AlessioSavelli/Controllo-Accessi/Firmware/Relese/Interfaccia Software/Risultato Finale.png

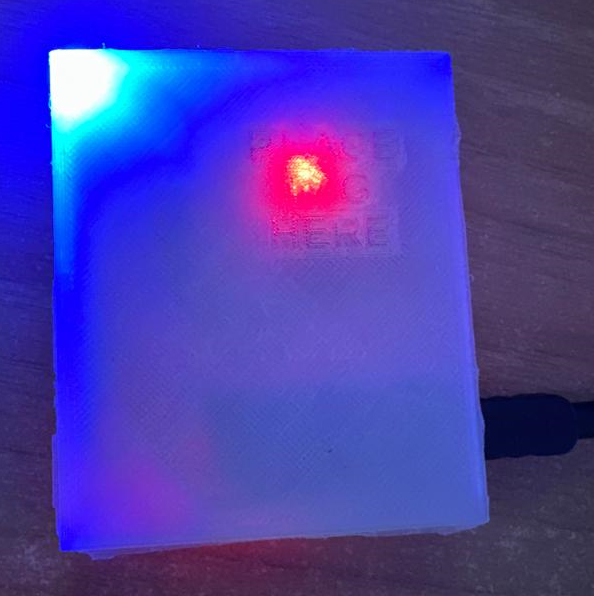
Firmware/Relese/Interfaccia Software/Risultato Finale.png
