AlessioSavelli/Controllo-Accessi/Firmware/Relese/Interfaccia Software/Schema.jpg

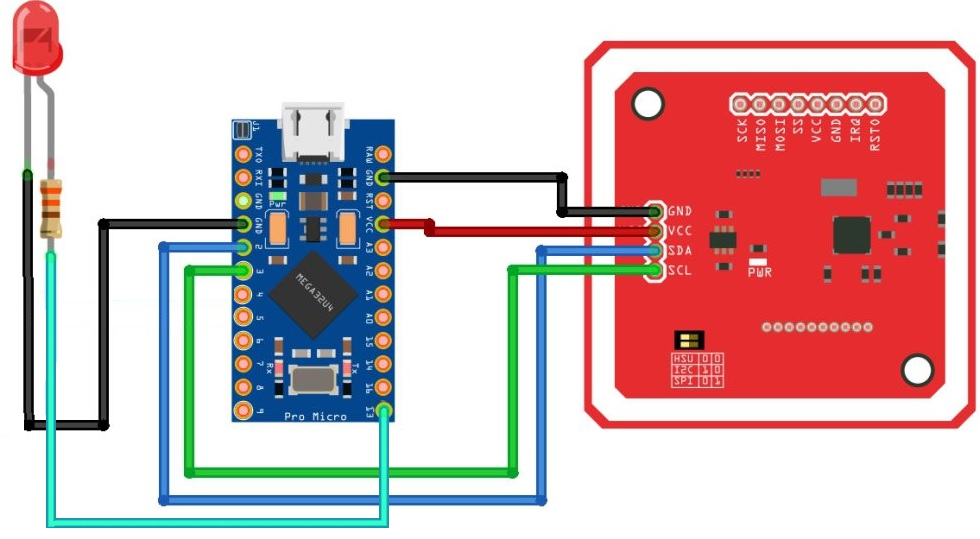
Firmware/Relese/Interfaccia Software/Schema.jpg
