AlessioSavelli/Controllo-Accessi/Firmware/Relese/V1.0.0/Main/Macro.h

/*    Macro di Alessio Savelli.       Create il 06/2022 e aggiornate al 01/2023
 *    Vers. : V1.0.1
 * Definisco delle macro generiche che vanno bene per tutto i moduli
 * N.B Ogni modulo/funzione può avere le sue macro specifiche solo per lei. Sono tutte dichiarata nei file .h o all'inizio delle funzioni
 */

//Definisco dei valori da uare per le macro
#define MACRO_TIMER_IS_NULL 0x00
#define MACRO_TIMER_INSTANTRIGGER_VALUE 0x01

#define MACRO_TIMER_TRIGER true
#define MACRO_TIMER_RUNING false

//----Definisco un Delay da usare per i core nel freertos---
#define TASKDELAY(MS) vTaskDelay(MS / portTICK_RATE_MS);
//------

//----Definisco Macro per gestire i timer----                                                                                             |ritorna true o false in base se il timer si triggera o no           |
#define IS_DELAYED(TIMER, MY_TIME) (((unsigned long)TIMER != MACRO_TIMER_IS_NULL) ? (((unsigned long)TIMER == MACRO_TIMER_INSTANTRIGGER_VALUE) ? MACRO_TIMER_TRIGER : ((millis() - ((unsigned long)TIMER)) >= MY_TIME)) : MACRO_TIMER_RUNING)  //Gestisce l'instant trigger e i timer inizializzati
#define START_TIMER(TIMER) (TIMER = millis())
#define STOP_TIMER(TIMER) (TIMER = MACRO_TIMER_IS_NULL)
#define ISALIVE_TIMER(TIMER) (TIMER != MACRO_TIMER_IS_NULL)
#define INSTANT_TRIGGER_TIMER(TIMER) (TIMER = MACRO_TIMER_INSTANTRIGGER_VALUE)  //Serve per avviare gia' il trigger del timer per la tempistica indicata in value
//-------------
//-----Definisco le macro per counter----
#define RESET_COUNTER(counter) (counter = 0)
//----
//----Definsico le macro per i buffer circolare---
#define CIRC_BUFFER_MULTISCROLL(index, scroll, maxItem) (index = (index + scroll) % maxItem)
#define CIRC_BUFFER_ONESCROLL(index, maxItem) (CIRC_BUFFER_MULTISCROLL(index, 1, maxItem))
#define REMOVE_FROM_INDEX(index, len) (index -= len)
#define ADD_TO_INDEX(index, len) (index += len)
//------
//-----Definisco le macro per gestire i bit----
#define BITMASK8(bitnum) (1 << bitnum)
#define GETBIT8(val, bitnum) ((val & BITMASK8(bitnum)) != 0)
#define BUILDBITMASK8(b7, b6, b5, b4, b3, b2, b1, b0) ((b0) | (b1 << 1) | (b2 << 2) | (b3 << 3) | (b4 << 4) | (b5 << 5) | (b6 << 6) | (b7 << 7))
#define CHECKBITMASK(val, bitmask) ((val & bitmask) == bitmask)
#define BITMASKRESET(bitmask) (bitmask = 0x00)
//----


//---Definisco macro per le conversione dei tempi
#define SECONDS 1000
#define MINUTES 60 * SECONDS
//------

//--Definisco macro per la conversione dei byte
#define KByte 1024
#define MByte 1024 * KByte
//----------

//--Definisco macro per la conversione in Hertz
#define KHz 1000
#define MHz 100000
//-----

//---Convert millis to format time
String _MY_MACRO_CONVERTION_TIME1(unsigned long time_to_convert) {
  unsigned long times = millis();
  int millisec = times % 100;
  int tseconds = times / 1000;
  int tminutes = tseconds / 60;
  int seconds = tseconds % 60;
  int thour = tminutes / 60;
  return "Time: " + String(thour, DEC) + ":" + String(tminutes, DEC) + ":" + String(seconds, DEC);
}

#define TIMEFORMAT_MILLIS _MY_MACRO_CONVERTION_TIME1(millis())
#define TIMEFORMAT_MILLIS_CHAR _MY_MACRO_CONVERTION_TIME1(millis()).c_str()

#define TIMEFORMAT_MYVALUE(val) _MY_MACRO_CONVERTION_TIME1(val)
#define TIMEFORMAT_MYVALUE_CHAR(val) _MY_MACRO_CONVERTION_TIME1(val).c_str()



//-----
